Dackara/Fil_Pilote/Image/Exemple/Fil_Pilote_3D_SinglePhase.png

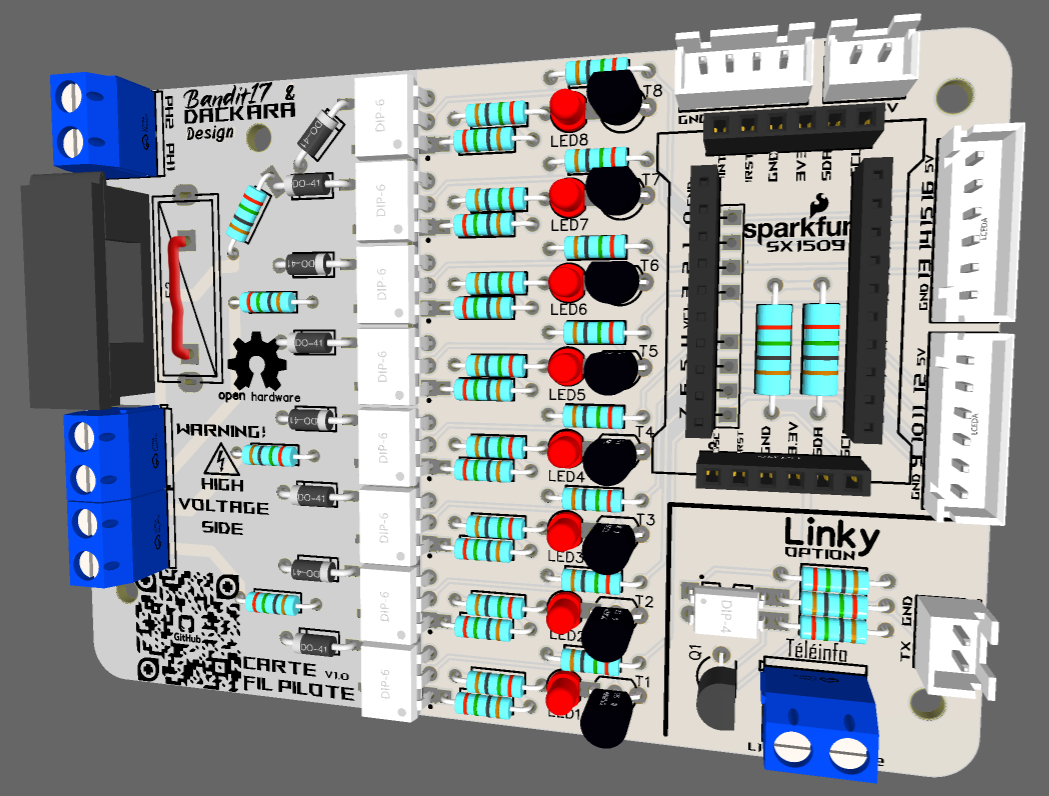
Image/Exemple/Fil_Pilote_3D_SinglePhase.png
