Dackara/Fil_Pilote/Image/Exemple/Fil_pilote_demo.png

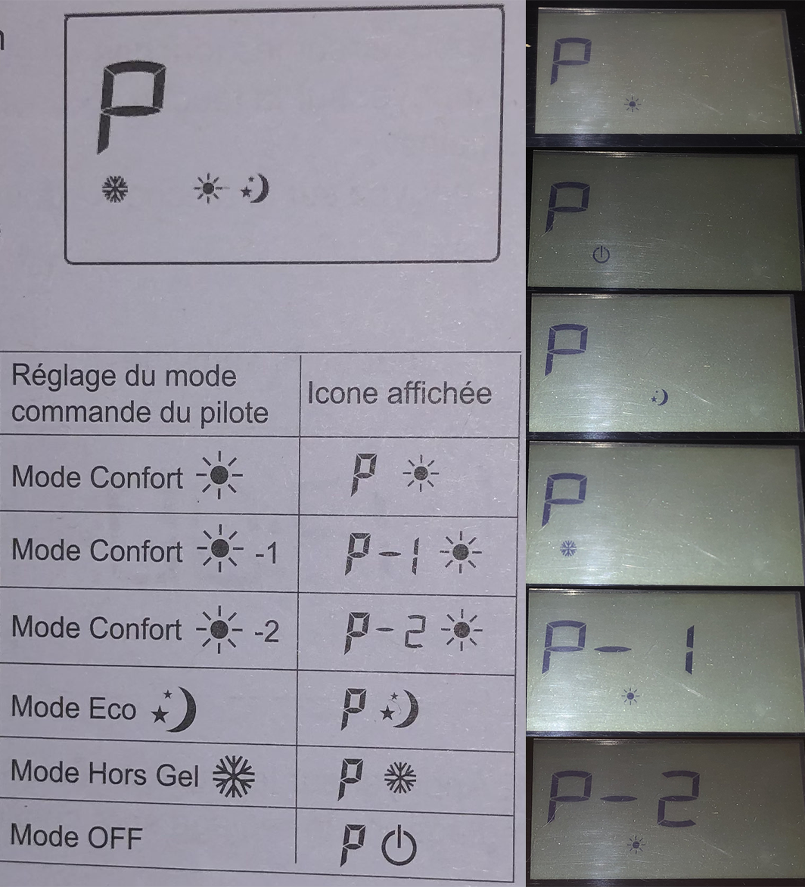
Image/Exemple/Fil_pilote_demo.png
