Dackara/Fil_Pilote/Image/Exemple/Signal_fil_pilote.png

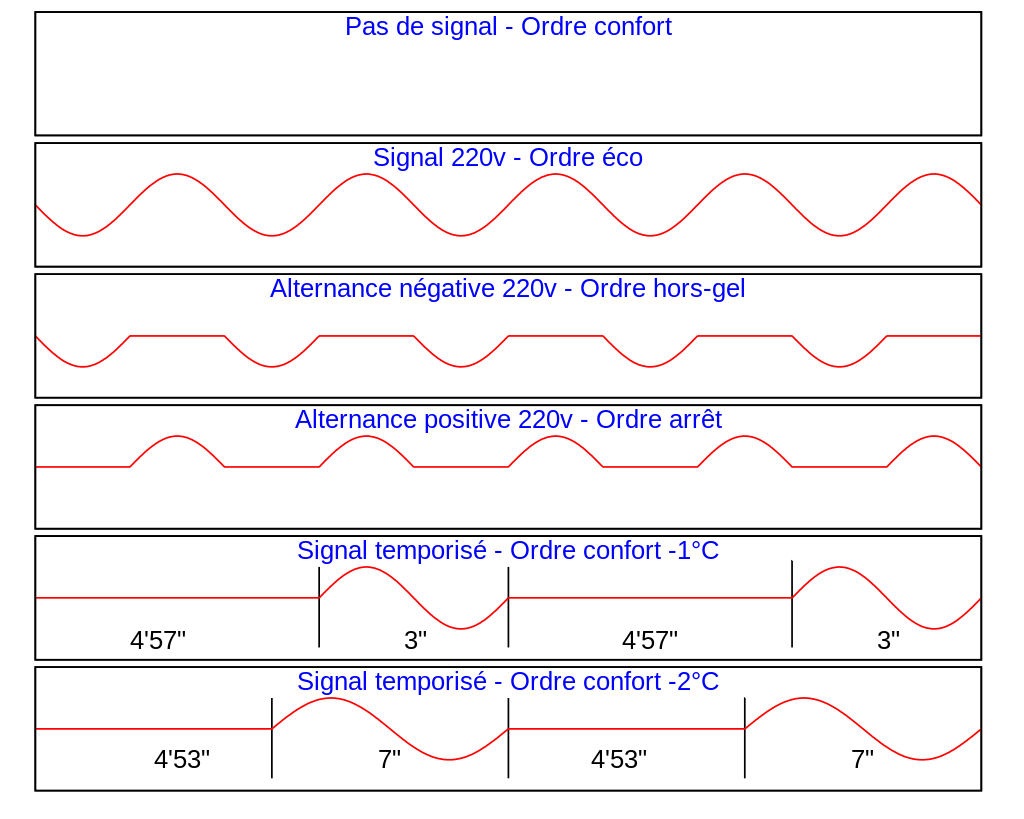
Image/Exemple/Signal_fil_pilote.png
