Dackara/Fil_Pilote/Hardware/3D_Print/Printed_time.png

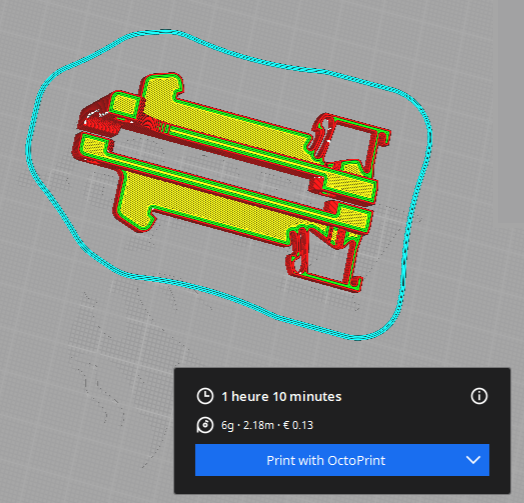
Hardware/3D_Print/Printed_time.png
